Yona-Appletree/AndymanCabinetsEsp32/src/renderer.cpp

//
// Created by Yona Appletree on 12/30/19.
//

#include "renderer.h"
#include "ui.h"

#define CABINET_LED_COUNT 72

extern std::vector<CabinetRing*> g_cabinetRings = {
	// North Cabinets (8)
	new CabinetRing {
		.host = "192.168.8.20",
		.cabinets = {
			new CabinetInfo(CABINET_LED_COUNT, TOP_LEFT, true, 1),
			new CabinetInfo(CABINET_LED_COUNT, TOP_RIGHT, false, 2),
			new CabinetInfo(CABINET_LED_COUNT, TOP_LEFT, true, 3),
			new CabinetInfo(CABINET_LED_COUNT, TOP_RIGHT, false, 4),
			new CabinetInfo(CABINET_LED_COUNT, TOP_LEFT, true, 5),
			new CabinetInfo(CABINET_LED_COUNT, TOP_RIGHT, true, 6),
			new CabinetInfo(CABINET_LED_COUNT, TOP_LEFT, false, 7),
			new CabinetInfo(CABINET_LED_COUNT, TOP_RIGHT, true, 8),
		}
	},

	// South Cabinets (4)
	new CabinetRing {
		.host = "192.168.8.21",
		.cabinets = {
			new CabinetInfo(CABINET_LED_COUNT, TOP_LEFT, false, 1),
			new CabinetInfo(CABINET_LED_COUNT, TOP_LEFT, true, 2),
			new CabinetInfo(CABINET_LED_COUNT, TOP_RIGHT, false, 3),
			new CabinetInfo(CABINET_LED_COUNT, TOP_LEFT, true, 4),
		}
	},
};


void rendererSetup() {
	Serial.println("Starting Renderer...");

	for (auto ring : g_cabinetRings) {
		ring->begin();
	}
}

void rendererLoop() {
	auto pVisualizationProgram = g_visualizationPrograms[g_uiState.programMode % g_visualizationPrograms.size()];
	auto pVisualizationEffect = g_visualizationEffects[g_uiState.effectMode % g_visualizationEffects.size()];

	static auto lastTime = g_uiState.time;
	auto deltaTime = g_uiState.time - lastTime;
	lastTime = g_uiState.time;

	for (auto ring : g_cabinetRings) {
		pVisualizationProgram->applyToRing(*ring, deltaTime);
		pVisualizationEffect->applyToRing(*ring, deltaTime);
		ring->swapBuffers();
	}
}

void rendererSend() {
	for (auto ring : g_cabinetRings) {
		ring->send();
	}
}

CabinetInfo::CabinetInfo(int ledCount, CabinetCorner startCorner, bool clockwise, int universe) {
	this->ledCount = ledCount;
	this->startCorner = startCorner;
	this->clockwise = clockwise;
	this->universe = universe;
	this->buffer = new CRGB[ledCount];
	this->buffer2 = new CRGB[ledCount];
}

CabinetInfo::~CabinetInfo() {
	delete buffer;
	delete buffer2;
}

CabinetSide CabinetInfo::startSide() const {
	switch (startCorner) {
		case TOP_LEFT:
			return clockwise
			       ? TOP
			       : LEFT;

		case TOP_RIGHT:
			return clockwise
			       ? RIGHT
			       : TOP;

		case BOTTOM_RIGHT:
			return clockwise
			       ? BOTTOM
			       : RIGHT;

		case BOTTOM_LEFT:
			return clockwise
			       ? LEFT
			       : BOTTOM;
	}
}

CabinetLedPos CabinetInfo::ledPos(int ledIndex) const {
	ledIndex = ledIndex % ledCount;

	int ledsPerSide = ledCount / 4;

	auto side = static_cast<CabinetSide>(
		(startSide() + (ledIndex / ledsPerSide) * (clockwise ? 1 : -1)) % 4
	);

	auto sideFraction = double(clockwise
	                           ? ledIndex % ledsPerSide
	                           : ledsPerSide - 1 - (ledIndex % ledsPerSide)) / ledsPerSide;

	switch (side) {
		case TOP:    return CabinetLedPos { .x = sideFraction, .y = -1 };
		case RIGHT:  return CabinetLedPos { .x = 1,            .y = 1 - sideFraction };
		case BOTTOM: return CabinetLedPos { .x = -1,           .y = sideFraction };
		case LEFT:   return CabinetLedPos { .x = -1,           .y = 1 - sideFraction };
	}
}

void CabinetInfo::fill(CRGB color) const {
	for (int i=0; i<ledCount; i++) {
		buffer[i] = color;
	}
}

void CabinetInfo::swapBuffers() {
	CRGB* temp = buffer;
	buffer = buffer2;
	buffer2 = temp;
}

double CabinetRing::cabinetAngle(int cabinet) {
	return TWO_PI * (double) cabinet / cabinets.size();
}

CabinetRingLedPos CabinetRing::ledPosInRing(int cabinetIndex, int ledIndex) const {
	auto ledPos = cabinets[cabinetIndex]->ledPos(ledIndex);

	// [-.5, .5] value for the x position
	auto ledXFrac = ledPos.x / 2;

	return CabinetRingLedPos {
		.angle = TWO_PI * (double(cabinetIndex) + ledXFrac) / cabinets.size(),
		.z = ledPos.y
	};
}

void CabinetRing::begin() {
	if (host != nullptr) {
		Serial.printf("\tConnecting to %s\n", host);
		sender.begin(host);
	}
}

/**
 * Borrowed From FastLED internal controller code. Basically computes a correction factor for various pixels and
 * lighting environments.
 */
static CRGB computeAdjustment(uint8_t scale, const CRGB & colorCorrection, const CRGB & colorTemperature) {
	CRGB adj(0,0,0);

	if(scale > 0) {
		for(uint8_t i = 0; i < 3; i++) {
			uint8_t cc = colorCorrection.raw[i];
			uint8_t ct = colorTemperature.raw[i];
			if(cc > 0 && ct > 0) {
				uint32_t work = (((uint32_t)cc)+1) * (((uint32_t)ct)+1) * scale;
				work /= 0x10000L;
				adj.raw[i] = work & 0xFF;
			}
		}
	}

	return adj;
}

void CabinetRing::send() {
	if (host == nullptr) {
		return;
	}

	uint8_t brightness = dim8_video(255 * (g_uiState.brightness));

	int maxLedCount = 0;
	for (auto cab : cabinets) {
		maxLedCount = std::max(maxLedCount, cab->ledCount);
	}

	auto * tempBuffer = new CRGB[maxLedCount];

	auto correction = computeAdjustment(
		brightness,
		0xF0C8F0,
		UncorrectedTemperature
	);

	for (auto cabinet : cabinets) {
		for (int i=0; i<cabinet->ledCount; i++) {
			tempBuffer[i] = cabinet->buffer[i].scale8(correction);
		}

		sender.set(
			cabinet->universe - 1,
			(uint8_t *) tempBuffer,
			cabinet->ledCount * 3
		);

		sender.send();
	}

	delete[] tempBuffer;
}

void CabinetRing::swapBuffers() {
	for (auto cab : cabinets) {
		cab->swapBuffers();
	}
}
