Yona-Appletree/AndymanCabinetsEsp32/src/presetPalettes.h

//
// Created by Yona Appletree on 1/1/20.
//

#ifndef ANDYMANCABINETSESP32_PRESETPALETTES_H
#define ANDYMANCABINETSESP32_PRESETPALETTES_H

#include <FastLED.h>

// Palette for https://colorzilla.com/gradient-editor/#ff0000+0,ff0000+3,bfbf00+13,bfbf00+24,00ff00+32,00ff00+39,00baba+47,00bcbc+54,0000ff+64,0000ff+68,bc00bc+80,bc00bc+85,ff0000+97,ff0000+100,ff1c1c+100
DEFINE_GRADIENT_PALETTE( niceRainbow ) {
	0, 255,   0,   0,
	7, 255,   0,   0,
	33, 191, 191,   0,
	61, 191, 191,   0,
	81,   0, 255,   0,
	99,   0, 255,   0,
	119,   0, 186, 186,
	137,   0, 188, 188,
	163,   0,   0, 255,
	173,   0,   0, 255,
	204, 188,   0, 188,
	216, 188,   0, 188,
	247, 255,   0,   0,
	255, 255,   0,   0,
	255, 255,  28,  28
};



DEFINE_GRADIENT_PALETTE(bhw3_32) {
	0,247,244,9,
	15,219,114,57,
	40,192,0,0,
	53,175,14,108,
	71,158,28,216,
	94,123,136,241,
	109,188,123,241,
	127,123,136,241,
	147,158,28,216,
	181,234,94,10,
	193,211,74,73,
	216,158,28,216,
	255,32,40,108,
};
DEFINE_GRADIENT_PALETTE(bhw1_01) {
	0,244,168,48,
	117,230,78,92,
	255,173,54,228,
};
DEFINE_GRADIENT_PALETTE(bhw2_xc) {
	0,56,30,68,
	58,89,0,130,
	122,103,0,86,
	158,205,57,29,
	183,223,117,35,
	219,241,177,41,
	255,247,247,35,
};
DEFINE_GRADIENT_PALETTE(bhw3_52) {
	0,114,22,105,
	45,118,22,85,
	99,201,45,67,
	132,238,187,70,
	175,232,85,34,
	201,232,56,59,
	255,5,0,4,
};
DEFINE_GRADIENT_PALETTE(bhw2_14) {
	0,0,0,64,
	45,0,0,128,
	79,64,64,255,
	119,128,128,255,
	158,64,64,255,
	209,0,0,128,
	255,0,0,64,
};
DEFINE_GRADIENT_PALETTE(bhw3_40) {
	0,7,7,7,
	43,53,25,73,
	76,76,15,46,
	109,214,39,108,
	127,255,156,191,
	165,194,73,212,
	204,120,66,242,
	255,93,29,90,
};
DEFINE_GRADIENT_PALETTE(bhw3_18) {
	0,46,43,74,
	30,80,61,166,
	48,148,184,232,
	63,75,126,183,
	81,10,54,151,
	117,170,154,252,
	145,21,65,68,
	175,148,188,126,
	196,114,198,60,
	234,52,98,70,
	255,0,9,6,
};

TProgmemRGBGradientPalette_bytes palettes[] = {niceRainbow, bhw3_32, bhw1_01, bhw2_xc, bhw3_52, bhw2_14, bhw3_40, bhw3_18};
char paletteNames[][8] = { "rainbow", "bhw3_32", "bhw1_01", "bhw2_xc", "bhw3_52", "bhw2_14", "bhw3_40", "bhw3_18" };
const uint16_t paletteCount = 8;

#endif //ANDYMANCABINETSESP32_PRESETPALETTES_H
