Yona-Appletree/AndymanCabinetsEsp32/src/network.h

//
// Created by Yona Appletree on 12/30/19.
//

#ifndef ANDYMANCABINETSESP32_NETWORK_H
#define ANDYMANCABINETSESP32_NETWORK_H

#endif //ANDYMANCABINETSESP32_NETWORK_H

void networkSetup();
void networkLoop();

extern bool g_ethConnected;
